absmach/s0/a0/modules/C3293147.step

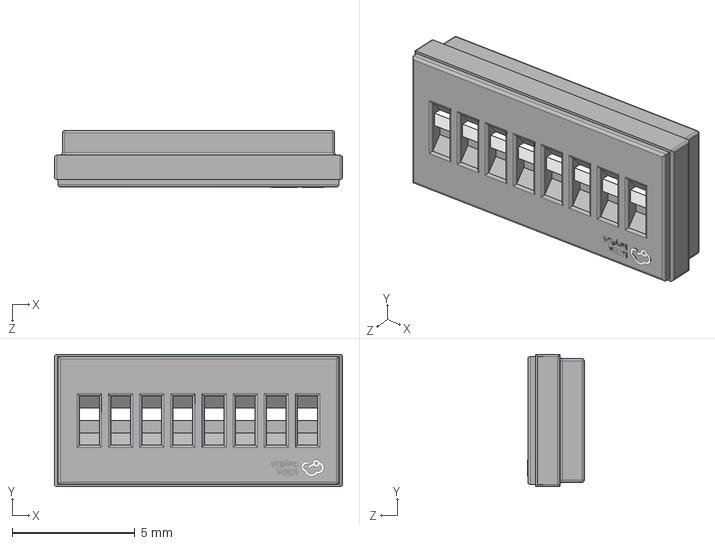
[picture p16: CAD file, 2026-07-27]
a0/modules/C3293147.step
11.7 x 5.40 x 2.31 mm
