absmach/s0/a0/modules/C5439767.step

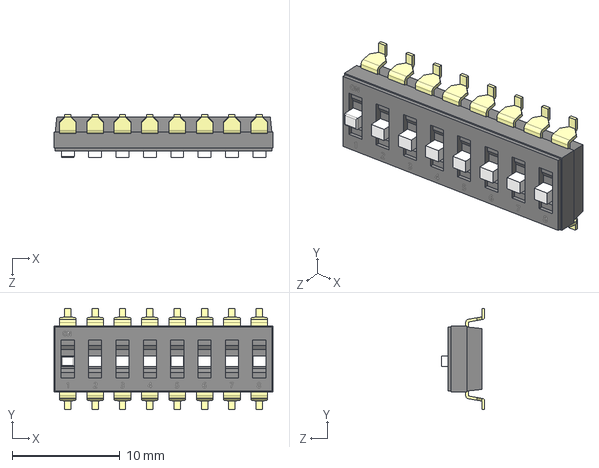
[picture p17: CAD file, 2026-07-27]
a0/modules/C5439767.step
20.3 x 9.40 x 4.00 mm
